ChitlangeSahas/UniWheel/Inventor CAD Files/Crown/tkor.jpg

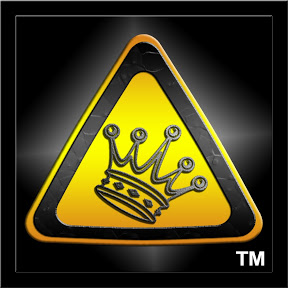
Inventor CAD Files/Crown/tkor.jpg
