ChitlangeSahas/UniWheel/Inventor CAD Files/Electronics/lolin-nodemcu-esp8266-development-board-v3-1.snapshot.3/Lolin NodeMCU ESP8266 V3 - ISO.JPG

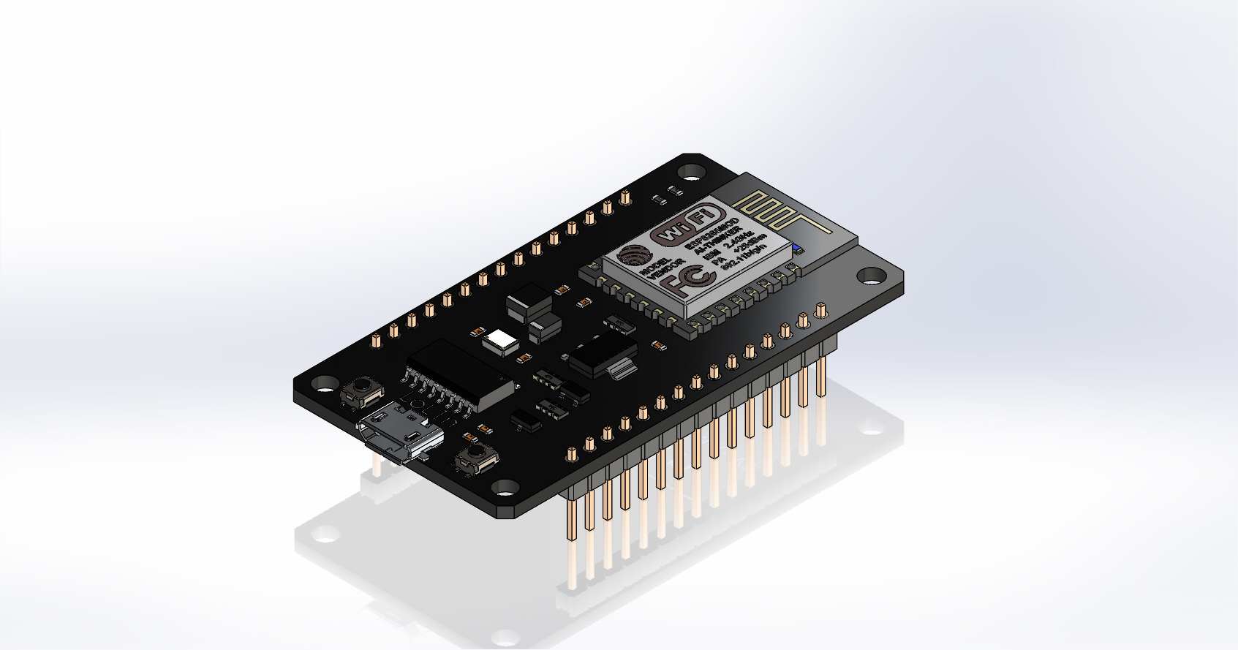
Inventor CAD Files/Electronics/lolin-nodemcu-esp8266-development-board-v3-1.snapshot.3/Lolin NodeMCU ESP8266 V3 - ISO.JPG
