ChitlangeSahas/UniWheel/Inventor CAD Files/Renders/Unicycle.png

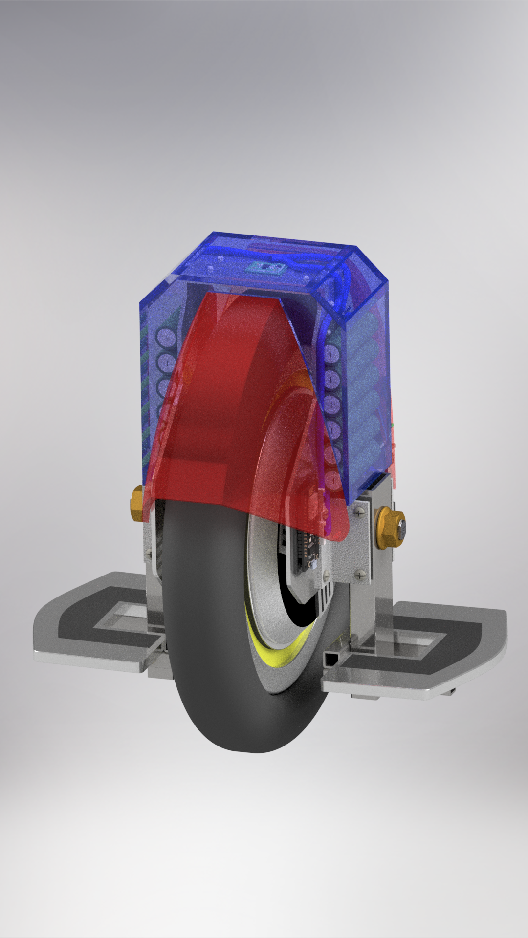
Inventor CAD Files/Renders/Unicycle.png
