ChitlangeSahas/UniWheel/Inventor CAD Files/Renders/Unicycle_80_.png

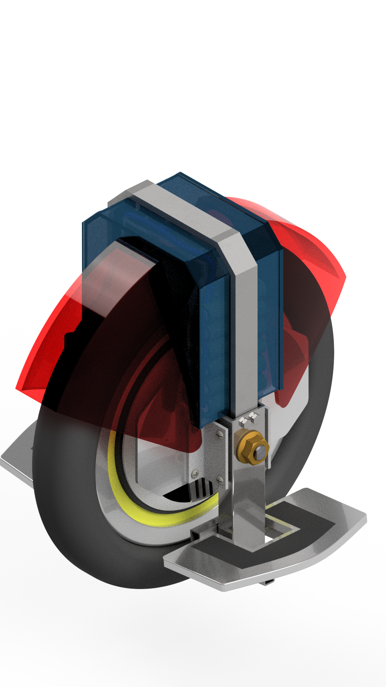
Inventor CAD Files/Renders/Unicycle_80_.png
