ChitlangeSahas/UniWheel/Inventor CAD Files/Renders/Unicycle_94.png

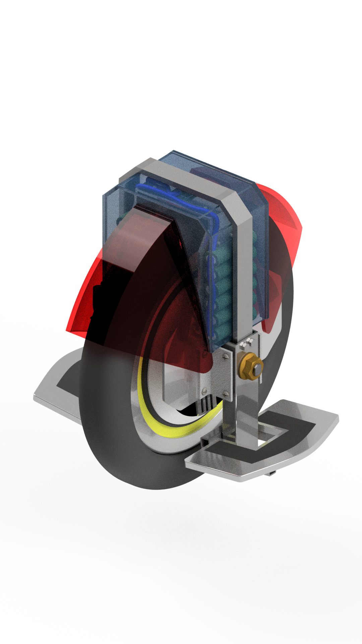
Inventor CAD Files/Renders/Unicycle_94.png
