ChitlangeSahas/UniWheel/Inventor CAD Files/Renders/Unicycle_115.png

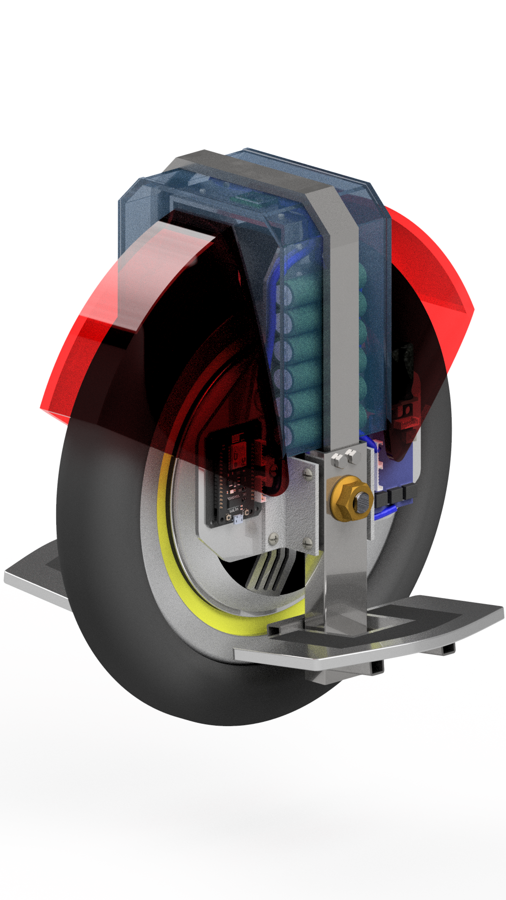
Inventor CAD Files/Renders/Unicycle_115.png
