ChitlangeSahas/UniWheel/Inventor CAD Files/Renders/Unicycle_173.png

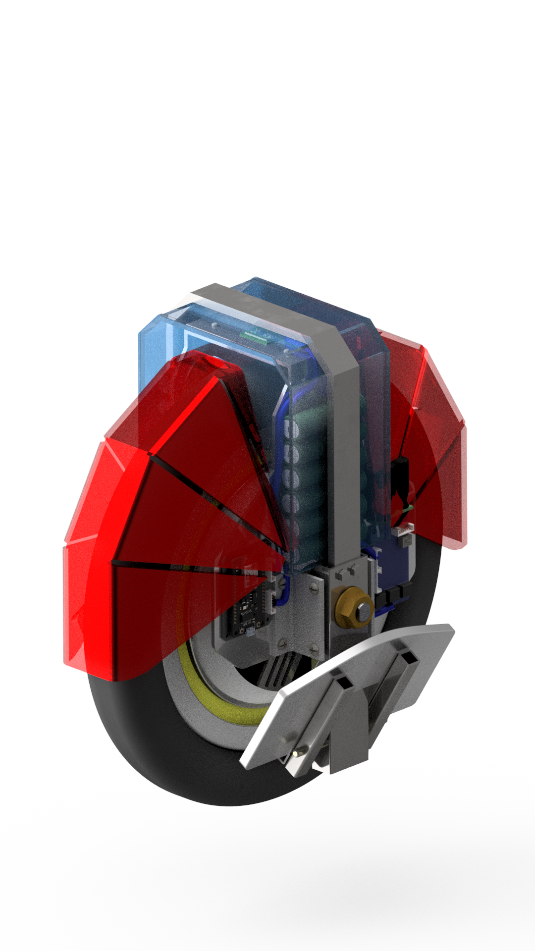
Inventor CAD Files/Renders/Unicycle_173.png
