ChitlangeSahas/UniWheel/Inventor CAD Files/Renders/Unicycle_182.png

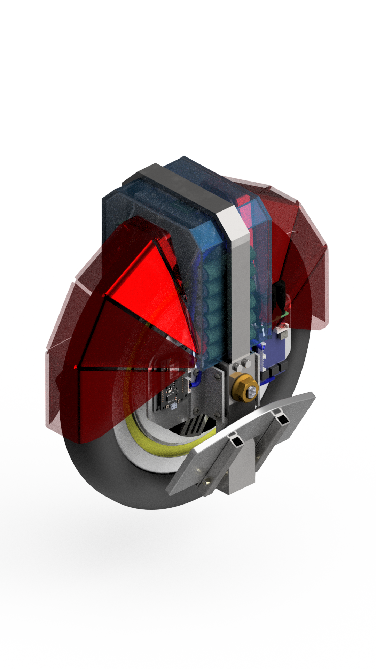
Inventor CAD Files/Renders/Unicycle_182.png
