ChitlangeSahas/UniWheel/Inventor CAD Files/Renders/Unicycle_1047.png

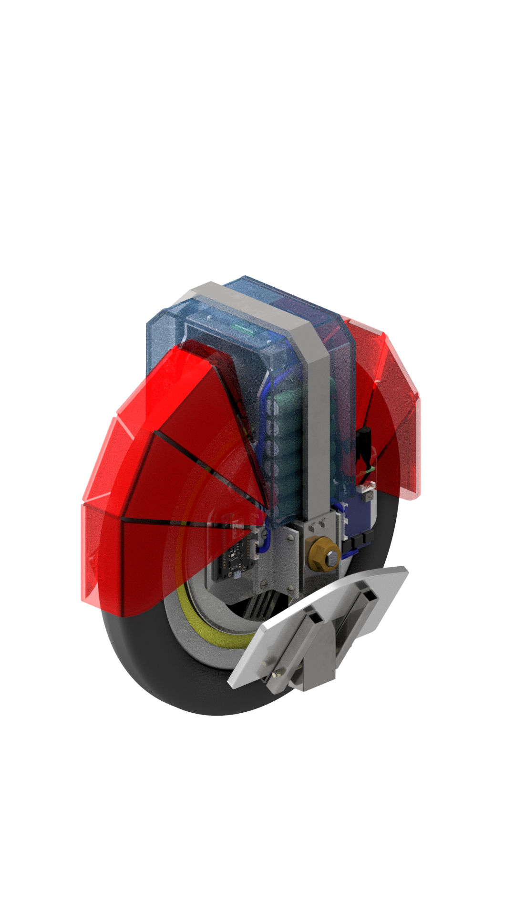
Inventor CAD Files/Renders/Unicycle_1047.png
