ChitlangeSahas/UniWheel/Inventor CAD Files/Renders/Unicycle_front.png

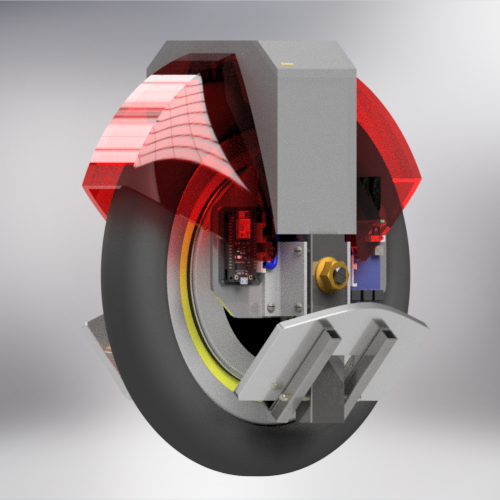
Inventor CAD Files/Renders/Unicycle_front.png
