ChitlangeSahas/UniWheel/Inventor CAD Files/Renders/Unicycle_Front_50.png

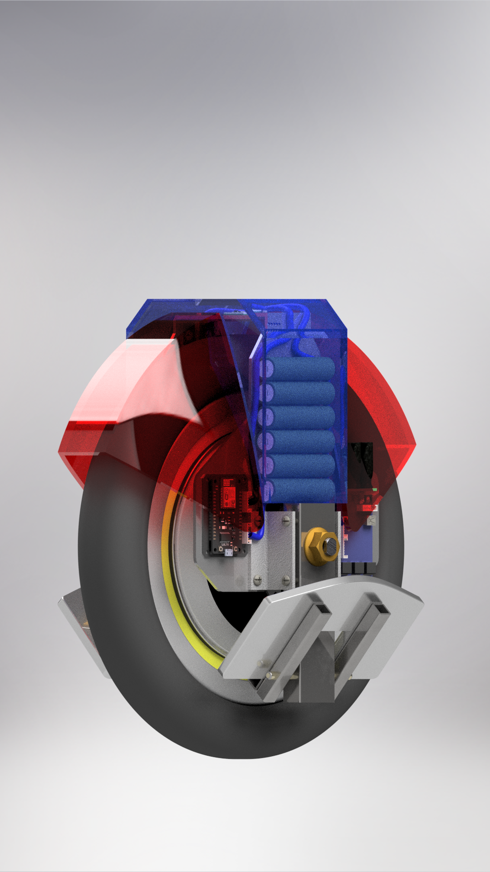
Inventor CAD Files/Renders/Unicycle_Front_50.png
