ChitlangeSahas/UniWheel/Inventor CAD Files/Renders/Unicycle_futuristic_55.png

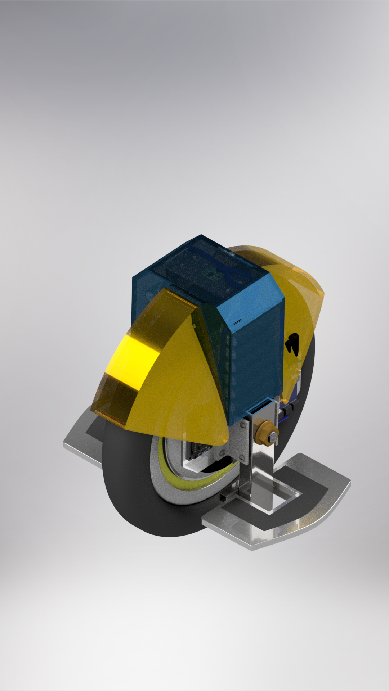
Inventor CAD Files/Renders/Unicycle_futuristic_55.png
