ChitlangeSahas/UniWheel/Inventor CAD Files/Battery Cover/Battery Cover v1 - Side.dxf

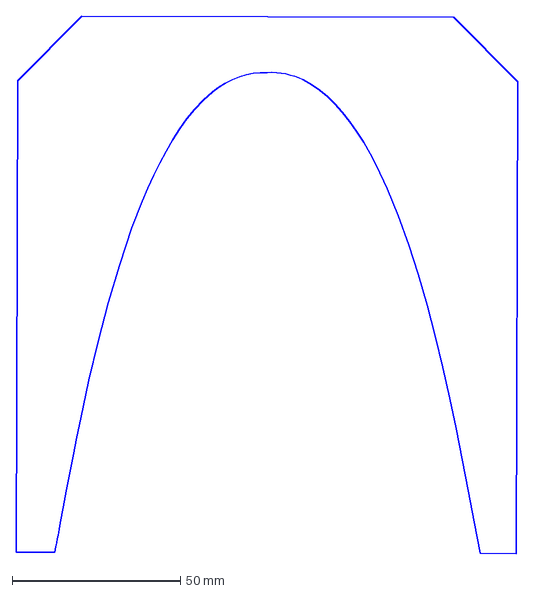
[picture p89: CAD file, 2019-12-15]
Inventor CAD Files/Battery Cover/Battery Cover v1 - Side.dxf
148.9 x 159.5 mm
