ChitlangeSahas/UniWheel/Inventor CAD Files/Electronics/JST Socket 7 Pin.step

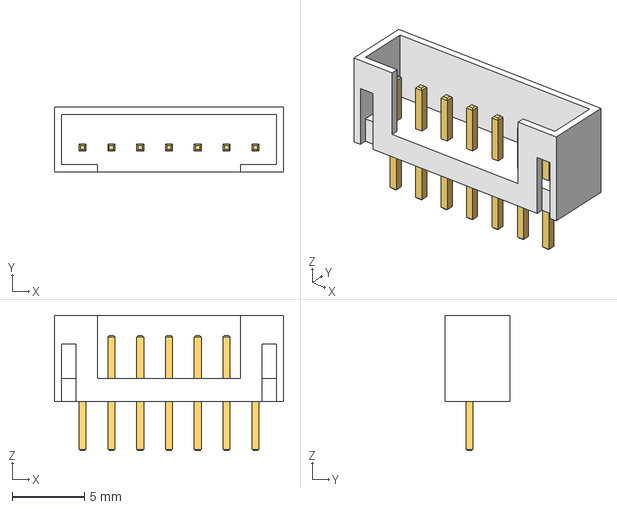
[picture p90: CAD file, 2019-12-15]
Inventor CAD Files/Electronics/JST Socket 7 Pin.step
15.9 x 4.50 x 9.40 mm
