ChitlangeSahas/UniWheel/Inventor CAD Files/Electronics/jst-ph-sockets-3-to-10-pins-1.snapshot.3/JST Socket 3 Pin.step

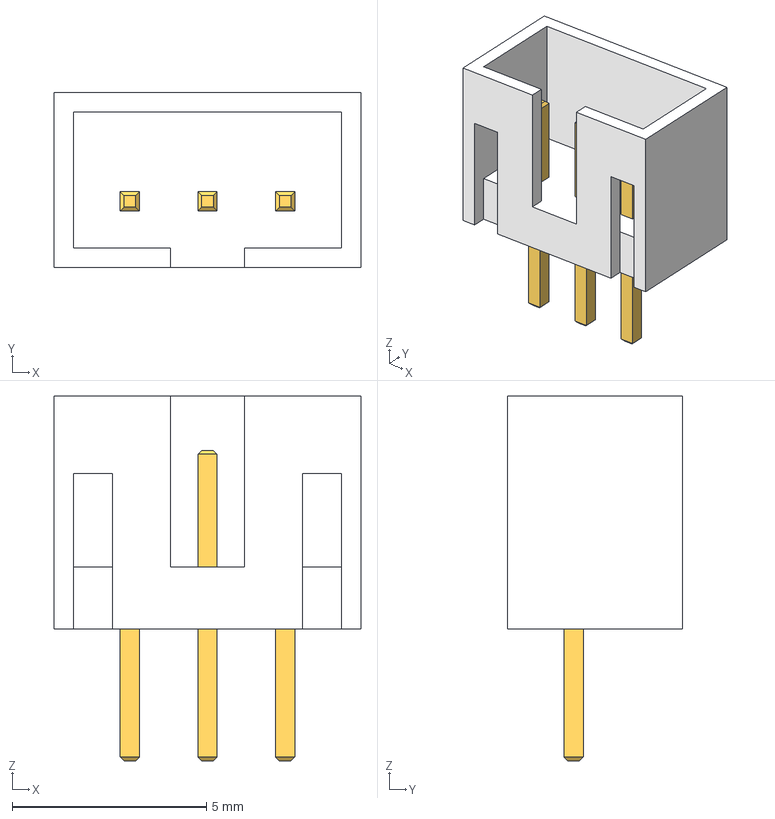
[picture p91: CAD file, 2019-12-15]
Inventor CAD Files/Electronics/jst-ph-sockets-3-to-10-pins-1.snapshot.3/JST Socket 3 Pin.step
7.90 x 4.50 x 9.40 mm
