ChitlangeSahas/UniWheel/Inventor CAD Files/Battery Cover/Solid1.dxf

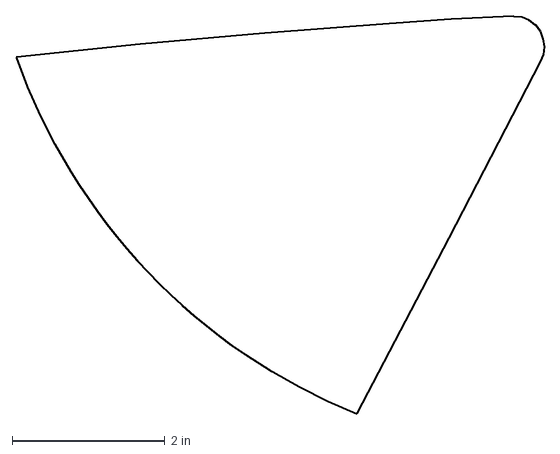
[picture p92: CAD file, 2019-12-15]
Inventor CAD Files/Battery Cover/Solid1.dxf
6.91 x 5.21 in
