ChitlangeSahas/UniWheel/Inventor CAD Files/Electronics/JST Socket 6 Pin.step

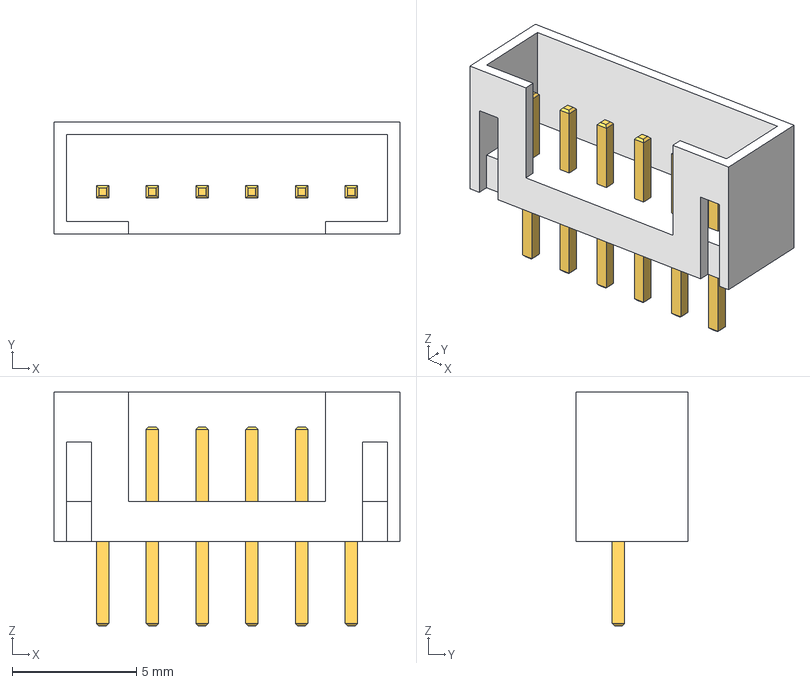
[picture p93: CAD file, 2019-12-15]
Inventor CAD Files/Electronics/JST Socket 6 Pin.step
13.9 x 4.50 x 9.40 mm
