ChitlangeSahas/UniWheel/Inventor CAD Files/Battery Cover/Shell.step

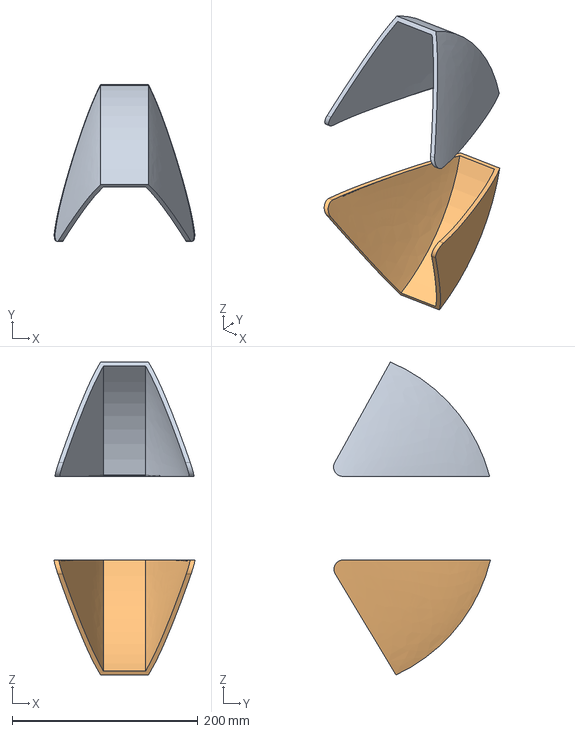
[picture p94: CAD file, 2019-12-15]
Inventor CAD Files/Battery Cover/Shell.step
151.3 x 168.9 x 336.8 mm
