ChitlangeSahas/UniWheel/Inventor CAD Files/Electronics/Gyro_box_bottom.stl

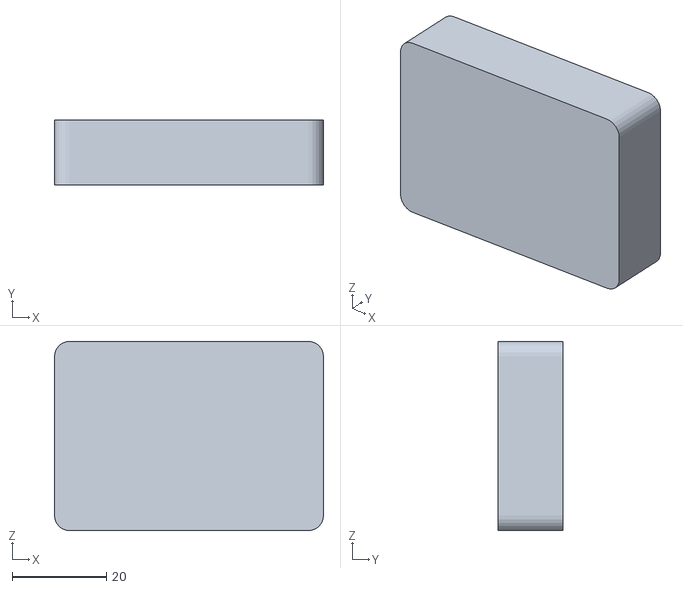
[picture p96: CAD file, 2019-12-15]
Inventor CAD Files/Electronics/Gyro_box_bottom.stl
57.0 x 13.8 x 40.1
